ahsan105/Sim800_Kicad/db9-rs232-1.snapshot.3/Renderings/12-10-2558 9-58-21.jpg

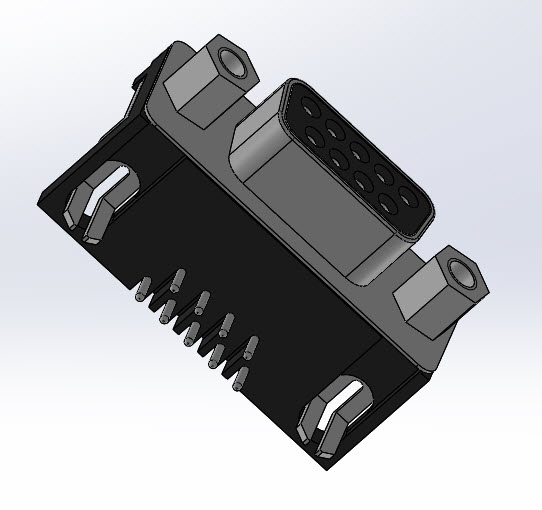
db9-rs232-1.snapshot.3/Renderings/12-10-2558 9-58-21.jpg
